Arthur-Sebastian/led-neon-lounge/resource_3d/stl_shapes/flamingo_2.stl

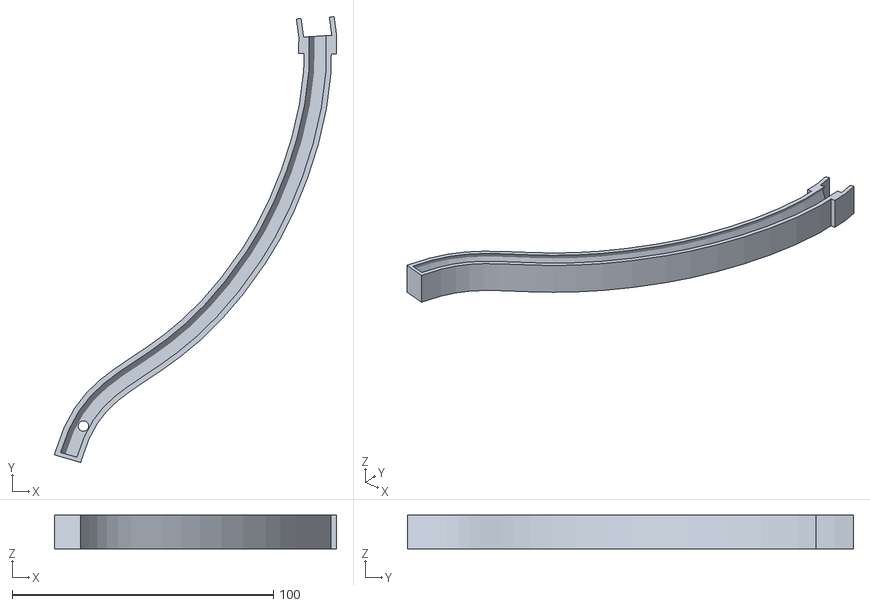
[picture p16: CAD file, 2021-12-19]
resource_3d/stl_shapes/flamingo_2.stl
108.0 x 170.6 x 13.0
