Arthur-Sebastian/led-neon-lounge/resource_3d/stl_shapes/garnish_1.stl

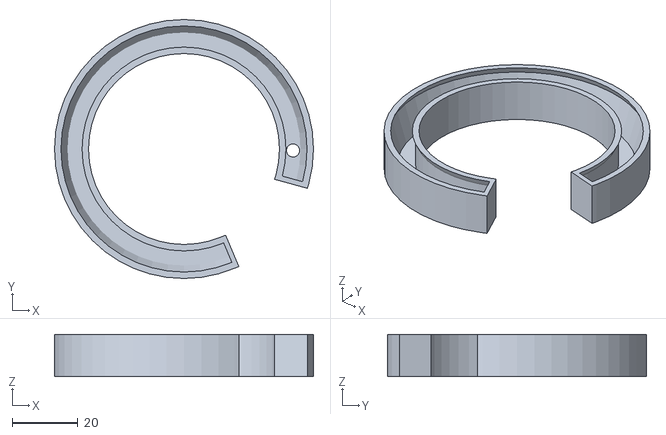
[picture p17: CAD file, 2021-12-19]
resource_3d/stl_shapes/garnish_1.stl
79.0 x 79.0 x 12.8
