Arthur-Sebastian/led-neon-lounge/resource_3d/stl_shapes/flamingo_1.stl

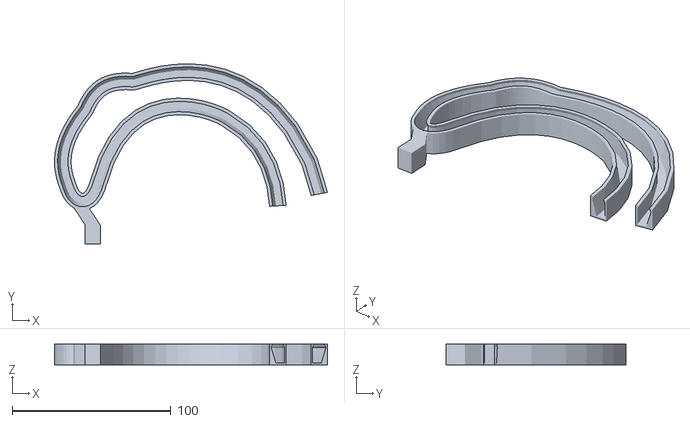
[picture p18: CAD file, 2021-12-19]
resource_3d/stl_shapes/flamingo_1.stl
172.1 x 113.7 x 13.0
