Arthur-Sebastian/led-neon-lounge/resource_3d/stl_shapes/palm_3.stl

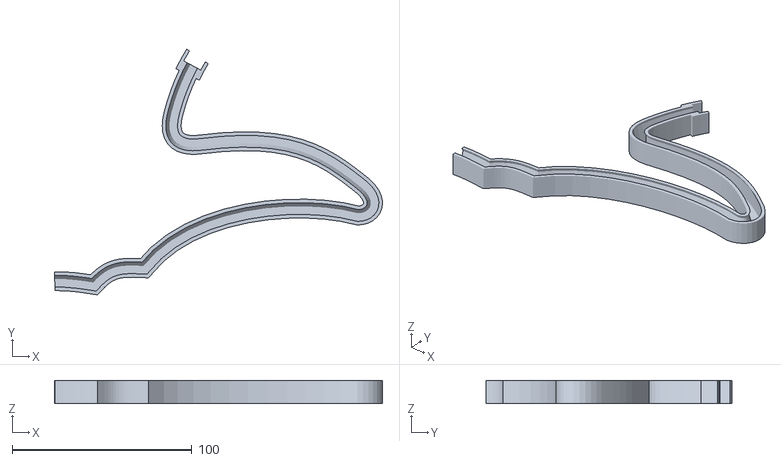
[picture p19: CAD file, 2021-12-19]
resource_3d/stl_shapes/palm_3.stl
182.5 x 136.8 x 13.0
