Arthur-Sebastian/led-neon-lounge/resource_3d/stl_shapes/lounge_3.stl

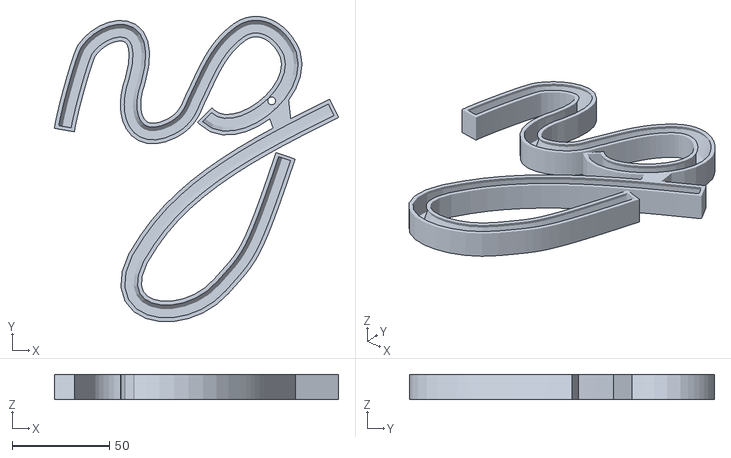
[picture p20: CAD file, 2021-12-19]
resource_3d/stl_shapes/lounge_3.stl
146.5 x 157.2 x 13.0
