Arthur-Sebastian/led-neon-lounge/resource_3d/stl_shapes/lounge_2.stl

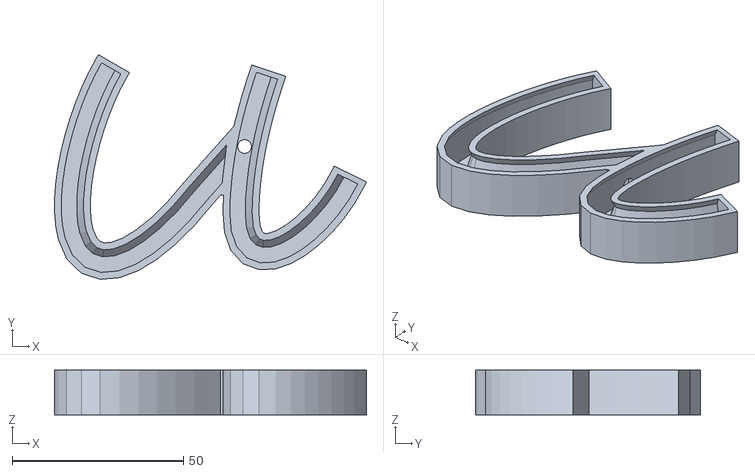
[picture p21: CAD file, 2021-12-19]
resource_3d/stl_shapes/lounge_2.stl
91.1 x 65.6 x 13.0
