Arthur-Sebastian/led-neon-lounge/resource_3d/stl_shapes/palm_6.stl

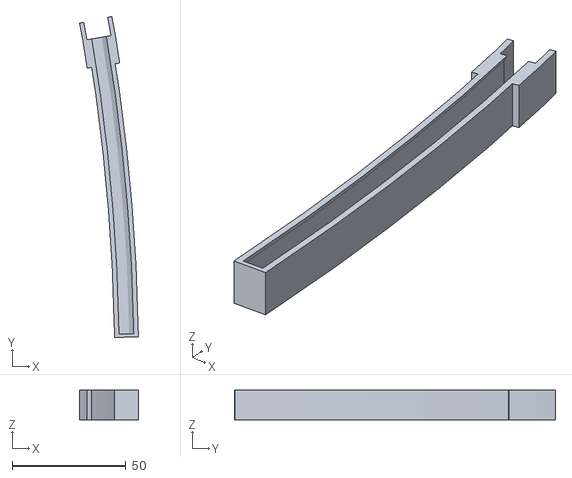
[picture p22: CAD file, 2021-12-19]
resource_3d/stl_shapes/palm_6.stl
25.9 x 141.1 x 13.0
