Arthur-Sebastian/led-neon-lounge/resource_3d/stl_shapes/palm_1.stl

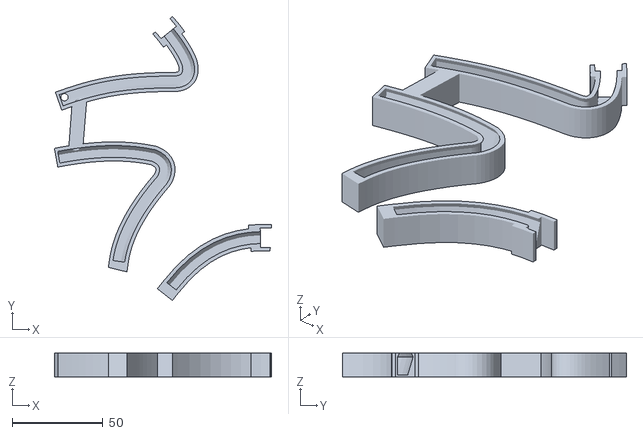
[picture p23: CAD file, 2021-12-19]
resource_3d/stl_shapes/palm_1.stl
119.5 x 156.2 x 13.0
