Arthur-Sebastian/led-neon-lounge/resource_3d/stl_shapes/lounge_4.stl

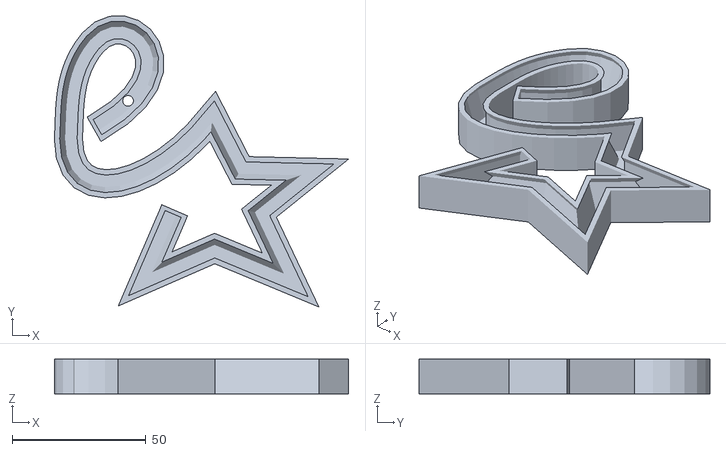
[picture p24: CAD file, 2021-12-19]
resource_3d/stl_shapes/lounge_4.stl
110.1 x 108.9 x 13.0
