Arthur-Sebastian/led-neon-lounge/resource_3d/stl_shapes/flamingo_3.stl

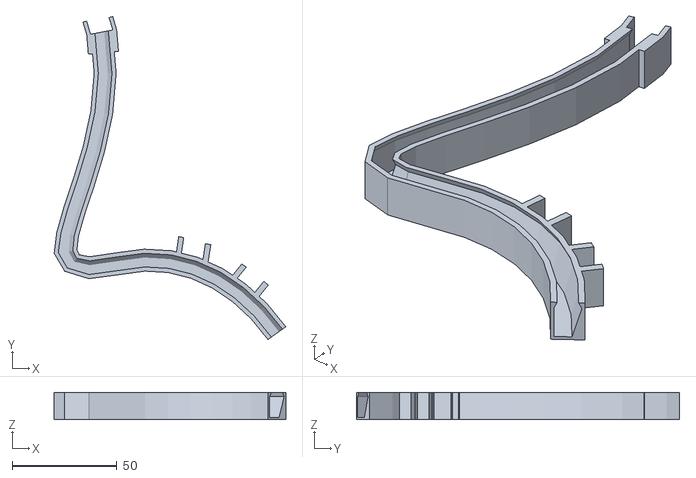
[picture p25: CAD file, 2021-12-19]
resource_3d/stl_shapes/flamingo_3.stl
110.6 x 154.2 x 13.0
