Arthur-Sebastian/led-neon-lounge/resource_3d/stl_shapes/flamingo_6.stl

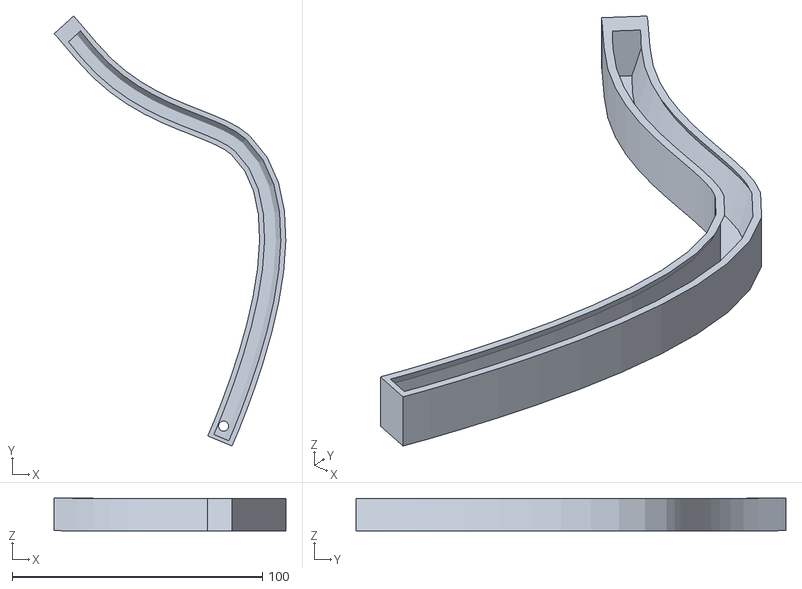
[picture p26: CAD file, 2021-12-19]
resource_3d/stl_shapes/flamingo_6.stl
92.5 x 171.7 x 13.0
