Arthur-Sebastian/led-neon-lounge/resource_3d/stl_shapes/lounge_1.stl

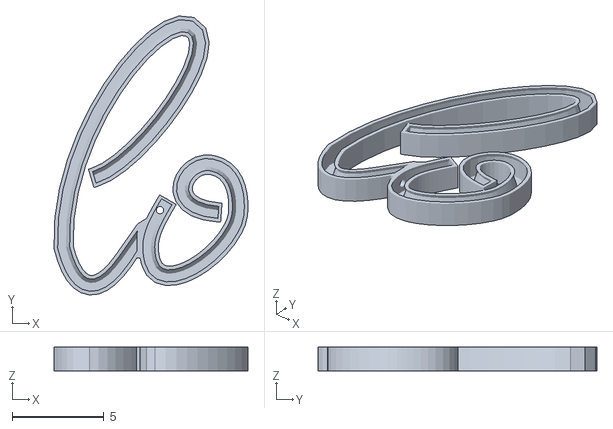
[picture p27: CAD file, 2021-12-19]
resource_3d/stl_shapes/lounge_1.stl
10.6 x 15.2 x 1.30
