Arthur-Sebastian/led-neon-lounge/resource_3d/stl_shapes/flamingo_4.stl

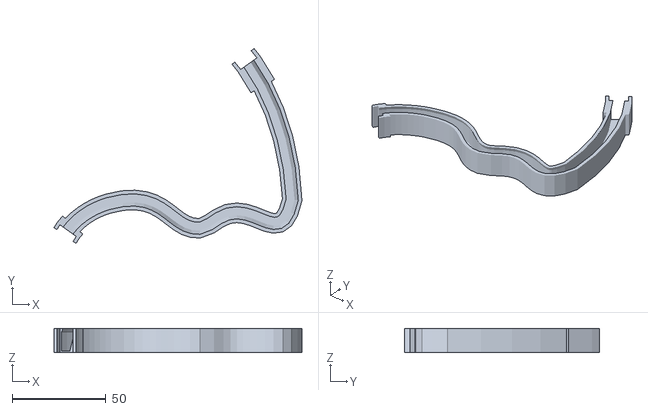
[picture p28: CAD file, 2021-12-19]
resource_3d/stl_shapes/flamingo_4.stl
132.5 x 104.1 x 13.0
