Arthur-Sebastian/led-neon-lounge/src/bootloaders/atmega16/atmega16_build_info.txt

Optiboot_flash build output for atmega16 
https://github.com/MCUdude/optiboot_flash 
Build date and time: 18.02.2019 00:06 
Compiler: avr-gcc 5.4.0
 
F_CPU:		UART NUMBER:	LED PIN:	LED FLASHES:	DESIRED BAUD:	ACTUAL BAUD:	ERROR:	COMPILED SIZE:	OUTPUT FILE:
24000000L	UART0		B0		2		1000000		1000000		0.0%	444 bytes	optiboot_flash_atmega16_UART0_1000000_24000000L.hex
24000000L	UART0		B0		2		500000		500000		0.0%	444 bytes	optiboot_flash_atmega16_UART0_500000_24000000L.hex
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
