Arthur-Sebastian/led-neon-lounge/src/color.cpp

#include "color.h"

const uint8_t hsv_sweep_r[400] PROGMEM =
{
	0xFF, 0xFD, 0xFB, 0xFA, 0xF8, 0xF7, 0xF5, 0xF3, 0xF2, 0xF0, 
	0xEF, 0xED, 0xEB, 0xEA, 0xE8, 0xE7, 0xE5, 0xE3, 0xE2, 0xE0, 
	0xDF, 0xDD, 0xDB, 0xDA, 0xD8, 0xD7, 0xD5, 0xD3, 0xD2, 0xD0, 
	0xCF, 0xCD, 0xCB, 0xCA, 0xC8, 0xC7, 0xC5, 0xC3, 0xC2, 0xC0, 
	0xBF, 0xBD, 0xBB, 0xBA, 0xB8, 0xB7, 0xB5, 0xB3, 0xB2, 0xB0, 
	0xAF, 0xAF, 0xAF, 0xAF, 0xAF, 0xAF, 0xAF, 0xAF, 0xAF, 0xAF, 
	0xAF, 0xAF, 0xAF, 0xAF, 0xAF, 0xAF, 0xAF, 0xAF, 0xAF, 0xAF, 
	0xAF, 0xAF, 0xAF, 0xAF, 0xAF, 0xAF, 0xAF, 0xAF, 0xAF, 0xAF, 
	0xAF, 0xAF, 0xAF, 0xAF, 0xAF, 0xAF, 0xAF, 0xAF, 0xAF, 0xAF, 
	0xAF, 0xAF, 0xAF, 0xAF, 0xAF, 0xAF, 0xAF, 0xAF, 0xAF, 0xAF, 
	0xAF, 0xAB, 0xA8, 0xA4, 0xA1, 0x9D, 0x9A, 0x96, 0x93, 0x8F, 
	0x8C, 0x88, 0x85, 0x81, 0x7E, 0x7A, 0x77, 0x73, 0x70, 0x6C, 
	0x69, 0x65, 0x62, 0x5E, 0x5B, 0x57, 0x54, 0x50, 0x4D, 0x49, 
	0x45, 0x42, 0x3F, 0x3B, 0x38, 0x34, 0x30, 0x2D, 0x2A, 0x26, 
	0x23, 0x1F, 0x1C, 0x18, 0x15, 0x11, 0x0E, 0x0A, 0x07, 0x03, 
	0x00, 0x00, 0x00, 0x00, 0x00, 0x00, 0x00, 0x00, 0x00, 0x00, 
	0x00, 0x00, 0x00, 0x00, 0x00, 0x00, 0x00, 0x00, 0x00, 0x00, 
	0x00, 0x00, 0x00, 0x00, 0x00, 0x00, 0x00, 0x00, 0x00, 0x00, 
	0x00, 0x00, 0x00, 0x00, 0x00, 0x00, 0x00, 0x00, 0x00, 0x00, 
	0x00, 0x00, 0x00, 0x00, 0x00, 0x00, 0x00, 0x00, 0x00, 0x00, 
	0x00, 0x00, 0x00, 0x00, 0x00, 0x00, 0x00, 0x00, 0x00, 0x00, 
	0x00, 0x00, 0x00, 0x00, 0x00, 0x00, 0x00, 0x00, 0x00, 0x00, 
	0x00, 0x00, 0x00, 0x00, 0x00, 0x00, 0x00, 0x00, 0x00, 0x00, 
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
	{
		output -> r = pgm_read_byte(&sine_full[v]);
		output -> g = pgm_read_byte(&sine_half[v]);
	}
	//second part, blue
	else if(v > sec2_beg && v < sec2_end)
	{
		uint16_t vt = v - sec2_beg;
		output -> g = pgm_read_byte(&sine_half[vt]);
		output -> b = pgm_read_byte(&sine_full[vt]);
	}
}

uint8_t pong_bitmask(uint16_t v, const uint8_t c)
{
	//temporary channel bitmask
	uint8_t ct = c;
	//make it periodic
	v %= 141;
	//only selected channels lit up, use bitmasks
	switch(v)
	{
		case 0 ... 10:
			ct &= 0b00000001;
			break;
		case 11 ... 20:
			ct &= 0b00000010;
			break; 
		case 21 ... 30:
			ct &= 0b00000100;
			break;
		case 31 ... 40:
			ct &= 0b00001000;
			break;
		case 41 ... 50:
			ct &= 0b00010000;
			break;
		case 51 ... 60:
			ct &= 0b00100000;
			break;
		case 61 ... 70:
			ct &= 0b00000000;
			break;
		case 71 ... 80:
			ct &= 0b00100000;
			break;
		case 81 ... 90:
			ct &= 0b00010000;
			break;
		case 91 ... 100:
			ct &= 0b00001000;
			break;
		case 101 ... 110:
			ct &= 0b00000100;
			break;
		case 111 ... 120:
			ct &= 0b00000010;
			break;
		case 121 ... 130:
			ct &= 0b00000001;
			break;
		case 131 ... 140:
			ct &= 0b00000000;
			break;
	}
	return ct;
}

void pong_multicolor(uint16_t v, const uint8_t c, color24* output)
{
	//prepare output register
	output -> r = 0;
	output -> g = 0;
	output -> b = 0;
	//apply bitmasks for selected channels
	uint8_t ct = pong_bitmask(v, c);
	//exit if no channel specified
	if(!ct) return;
	//apply correct colors
	switch(v)
	{
		//red
		case 0 ... 70:
			output -> r = 0xFF;
			break;
		//orange
		case 71 ... 140:
			output -> r = 0xFF;
			output -> g = 0x40;
			break;
		//yellow
		case 141 ... 210:
			output -> r = 0xFF;
			output -> g = 0x80;
			break;
		//green
		case 211 ... 280:
			output -> g = 0xFF;
			break;
		//cyan
		case 281 ... 350:
			output -> g = 0xFF;
			output -> b = 0x80;
			break;
		//blue
		case 351 ... 420:
			output -> b = 0xFF;
			break;
		//violet
		case 421 ... 490:
			output -> r = 0x80;
			output -> b = 0xFF;
			break;
		//pink
		case 491 ... 560:
			output -> r = 0xFF;
			output -> b = 0x80;
			break;
	}
}

void pong_white(uint16_t v, const uint8_t c, color24* output)
{
	//prepare output register
	output -> r = 0;
	output -> g = 0;
	output -> b = 0;
	//apply bitmasks for selected channels
	uint8_t ct = pong_bitmask(v, c);
	//exit if no channel specified
	if(!ct) return;
	output -> r = 0xFF;
	output -> g = 0xFF;
	output -> b = 0xFF;
}

void pong_magma(uint16_t v, const uint8_t c, color24* output)
{
	//prepare output register
	output -> r = 0;
	output -> g = 0;
	output -> b = 0;
	//apply bitmasks for selected channels
	uint8_t ct = pong_bitmask(v, c);
	//exit if no channel specified
	if(!ct) return;
	//apply colors
	switch(v)
	{
		//orange
		case 0 ... 70:
			output -> r = 0xFF;
			output -> g = 0x20;
			break;
		case 71 ... 140:
			output -> g = 0xFF;
			output -> b = 0xC0;
			break;
	}
}

void static_color(uint8_t index, color24* output)
{
	output -> r = pgm_read_byte(&static_color_r[index]);
	output -> g = pgm_read_byte(&static_color_g[index]);
	output -> b = pgm_read_byte(&static_color_b[index]);
}
