Arthur-Sebastian/led-neon-lounge/src/ir_buttons.h

/*
 * IR_Buttonmap.h
 *
 * Created: 13.07.2020 22:11:09
 *  Author: Artur
 */ 


#ifndef IR_BUTTONMAP_H_
#define IR_BUTTONMAP_H_

#define POWR_B 0x45
#define MENU_B 0x47
#define TEST_B 0x44
#define PLUS_B 0x40
#define BACK_B 0x43
#define REVD_B 0x07
#define PLAY_B 0x15
#define FRWD_B 0x09
#define NUM0_B 0x16
#define MINS_B 0x19
#define LTRC_B 0x0D
#define NUM1_B 0x0C
#define NUM2_B 0x18
#define NUM3_B 0x5E
#define NUM4_B 0x08
#define NUM5_B 0x1C
#define NUM6_B 0x5A
#define NUM7_B 0x42
#define NUM8_B 0x52
#define NUM9_B 0x4A

#endif /* IR_BUTTONMAP_H_ */
